Ribbit-Network/ribbit-network-frog-hardware/assembly-instructions/1-parts/images/electric_components.jpg

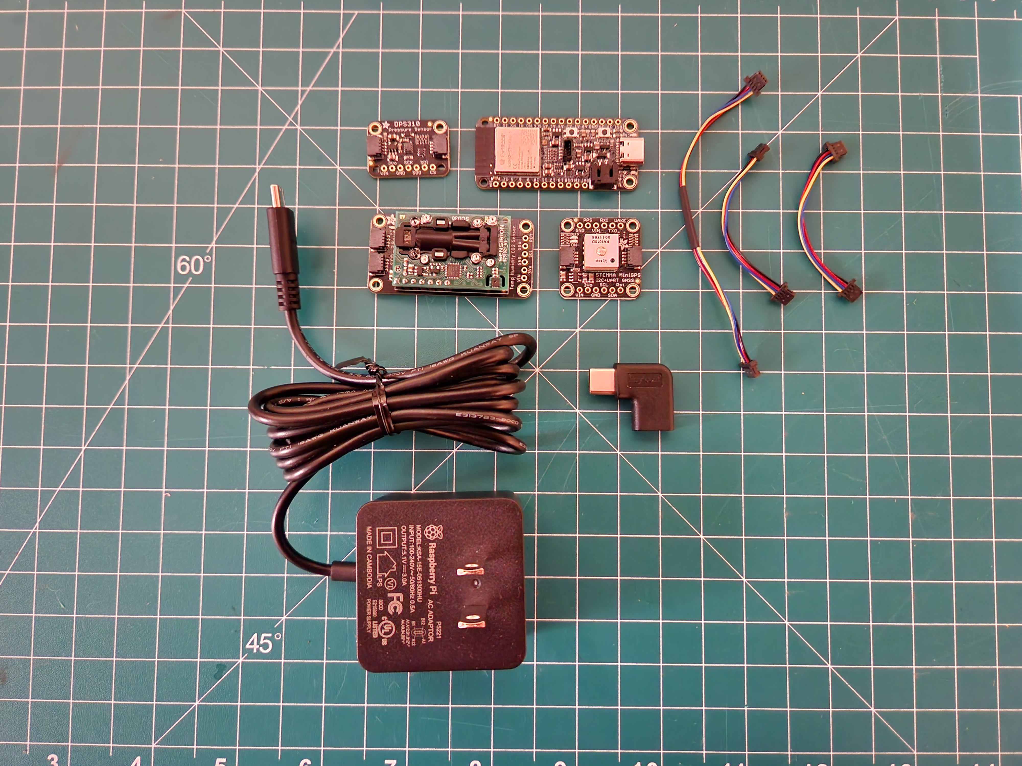
assembly-instructions/1-parts/images/electric_components.jpg
