Ribbit-Network/ribbit-network-frog-hardware/assembly-instructions/6-sensor-placement/images/postmount_back.jpg

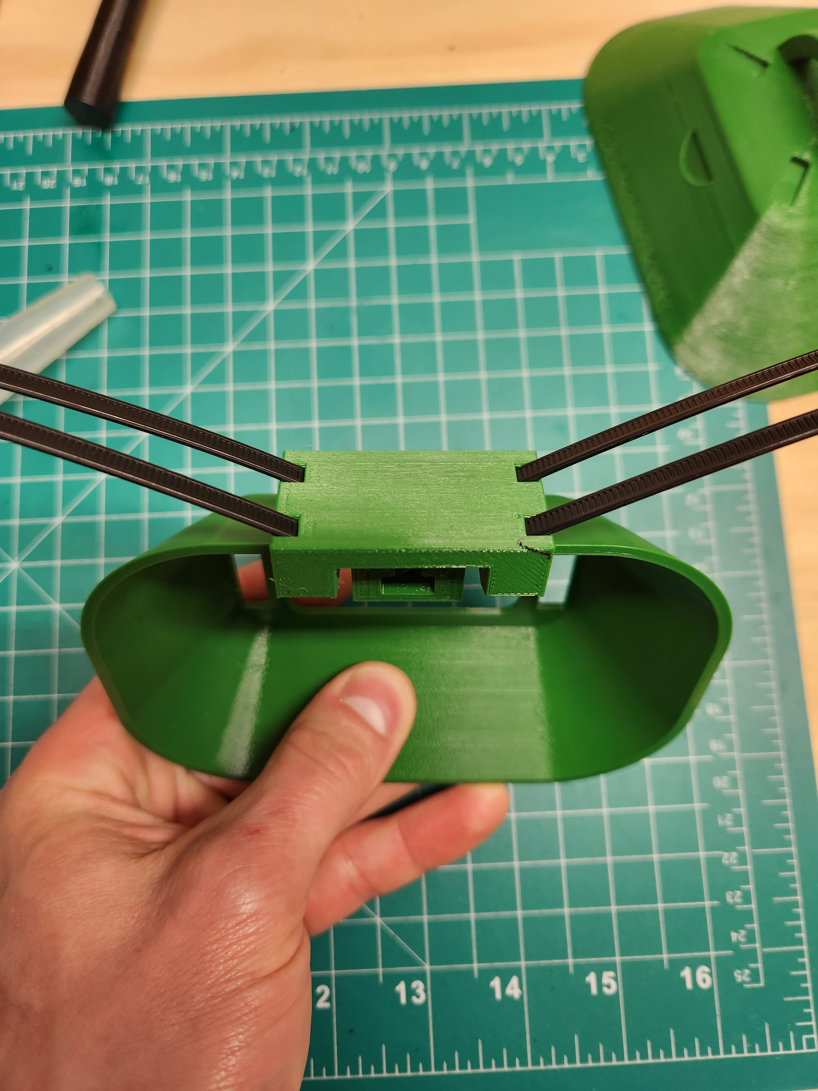
assembly-instructions/6-sensor-placement/images/postmount_back.jpg
