Ribbit-Network/ribbit-network-frog-hardware/assembly-instructions/images/ribbit_nice.png

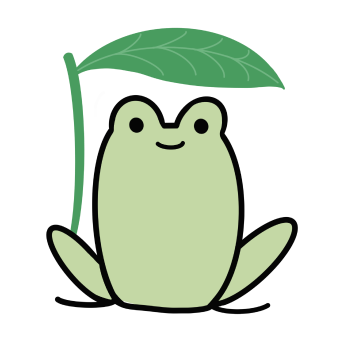
assembly-instructions/images/ribbit_nice.png
