Ribbit-Network/ribbit-network-frog-hardware/assembly-instructions/4-assembly/images/ziptie_option.jpg

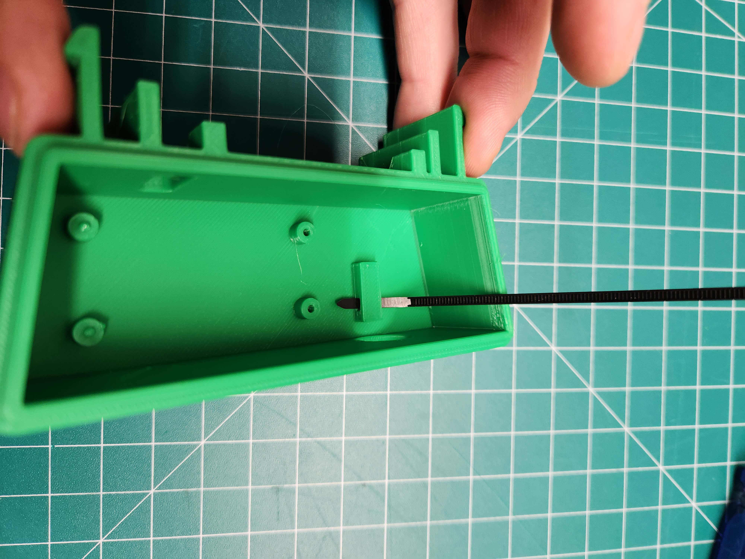
assembly-instructions/4-assembly/images/ziptie_option.jpg
